nlbutts/Foyers/software/backporch/Core/Src/app_freertos.c

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

/* Includes ------------------------------------------------------------------*/
#include "FreeRTOS.h"
#include "task.h"
#include "main.h"

/* Hook prototypes */
void configureTimerForRunTimeStats(void);
unsigned long getRunTimeCounterValue(void);
void vApplicationStackOverflowHook(xTaskHandle xTask, signed char *pcTaskName);

/* USER CODE BEGIN 1 */
/* Functions needed when configGENERATE_RUN_TIME_STATS is on */
__weak void configureTimerForRunTimeStats(void)
{

}

__weak unsigned long getRunTimeCounterValue(void)
{
return 0;
}
/* USER CODE END 1 */

/* USER CODE BEGIN 4 */
void vApplicationStackOverflowHook(xTaskHandle xTask, signed char *pcTaskName)
{
   /* Run time stack overflow checking is performed if
   configCHECK_FOR_STACK_OVERFLOW is defined to 1 or 2. This hook function is
   called if a stack overflow is detected. */
}
/* USER CODE END 4 */
