nlbutts/Foyers/software/bootloader/BootloaderLib/bootloader.h

#ifndef __BOOTLOADER_H
#define __BOOTLOADER_H

#include "main.h"
#include <stdint.h>

#include "common.h"

/* WPILib CAN Addressing Constants */
#define WPILIB_DEVICE_ID (0) // Default Device ID

/* Memory Map Constants */
#define APP_START_ADDR 0x08008000
#define APP_SIZE_MAX (96 * 1024)
#define RAM_BUFFER_ADDR 0x2000C000

/* Bootloader State Machine */
typedef enum {
  BOOT_STATE_IDLE,
  BOOT_STATE_RECEIVING,
  BOOT_STATE_VERIFYING,
  BOOT_STATE_FLASHING,
  BOOT_STATE_COMPLETE,
  BOOT_STATE_ERROR
} BootloaderState_t;

/* Public Function Prototypes */
void Bootloader_Init(void);
void Bootloader_Loop(void);
void Bootloader_RxCallback(void);
void Bootloader_CheckAndJump(void);

#endif /* __BOOTLOADER_H */
